openenergymonitor/emontx4/docs/img/6CT/EmonTx4DB_rf.png

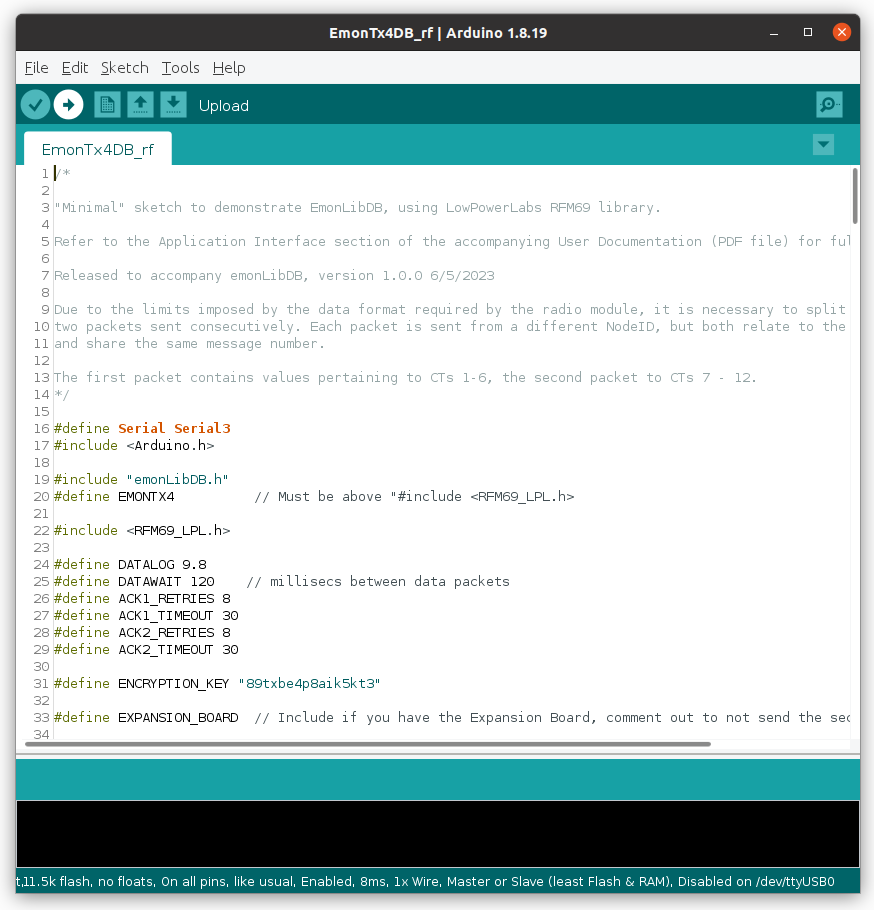
docs/img/6CT/EmonTx4DB_rf.png
