openenergymonitor/emontx4/docs/img/emontx4_serial_config_tool.png

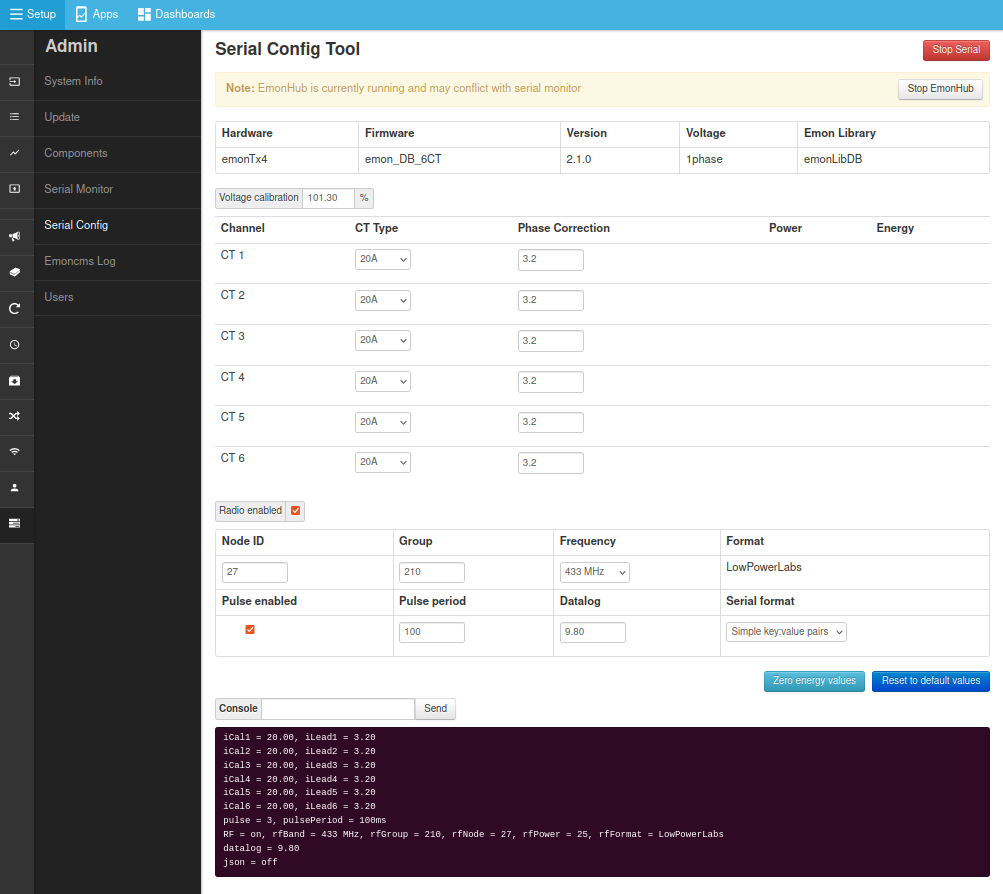
docs/img/emontx4_serial_config_tool.png
