openenergymonitor/emontx4/docs/img/heatpump/heatpump_ct_sensor_placements.png

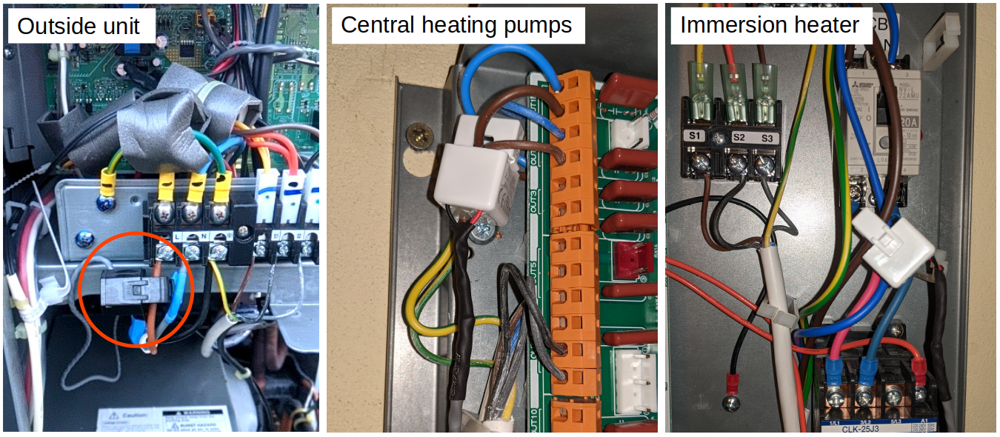
docs/img/heatpump/heatpump_ct_sensor_placements.png
