openenergymonitor/emontx4/docs/img/heatpump/temperature_sensor_02.jpg

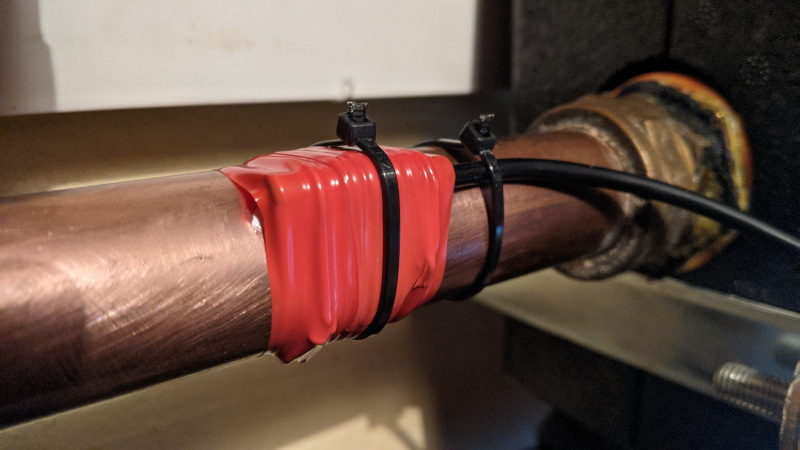
docs/img/heatpump/temperature_sensor_02.jpg
